ubilab-escape/mission-briefing/Briefing Clip/(Footage)/01. Edit Comp/Images/freelance-illustrator-peter-henderson-scifi.gif

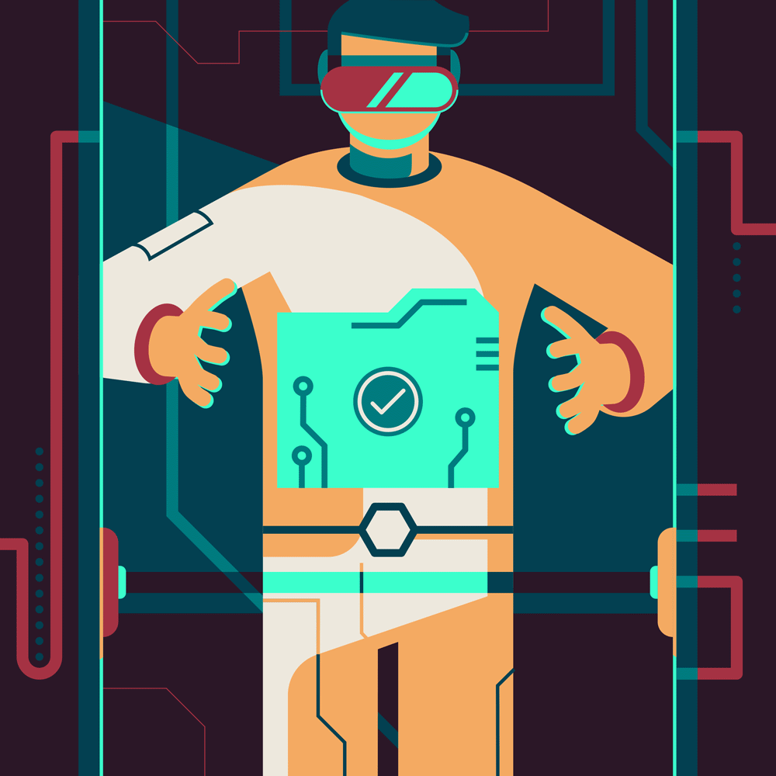
Briefing Clip/(Footage)/01. Edit Comp/Images/freelance-illustrator-peter-henderson-scifi.gif
