ubilab-escape/mission-briefing/CAD/Images/1.PNG

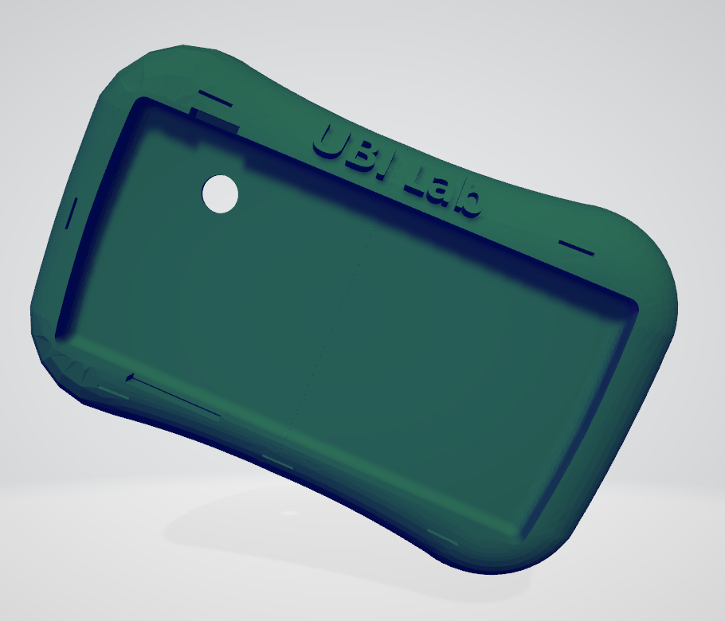
CAD/Images/1.PNG
