ubilab-escape/mission-briefing/CAD/Images/2.PNG

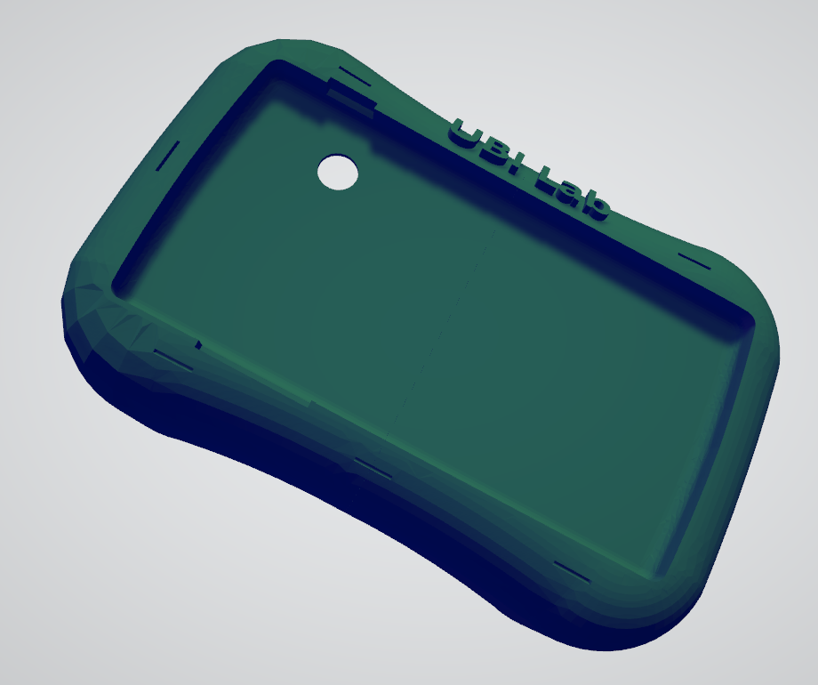
CAD/Images/2.PNG
