ubilab-escape/mission-briefing/CAD/Images/3.PNG

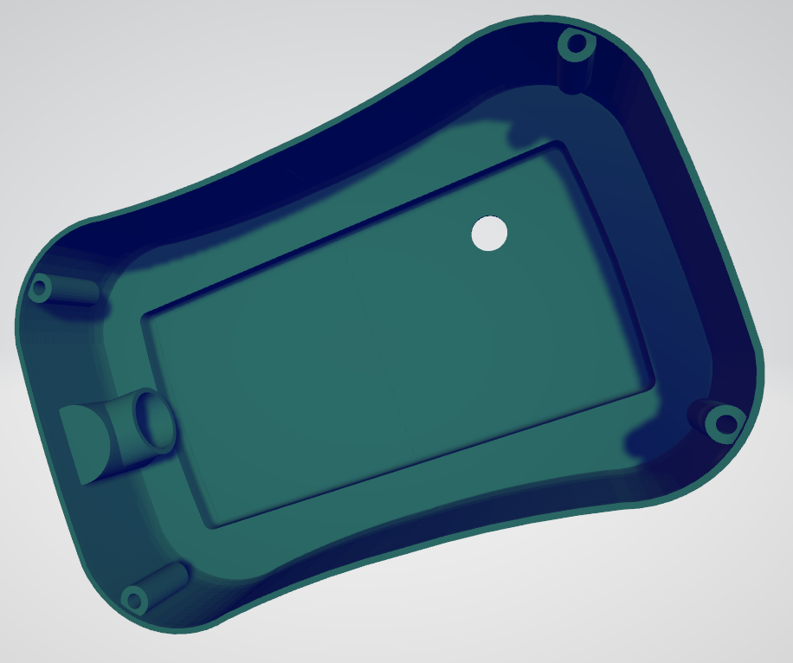
CAD/Images/3.PNG
