ubilab-escape/mission-briefing/CAD/Images/4.PNG

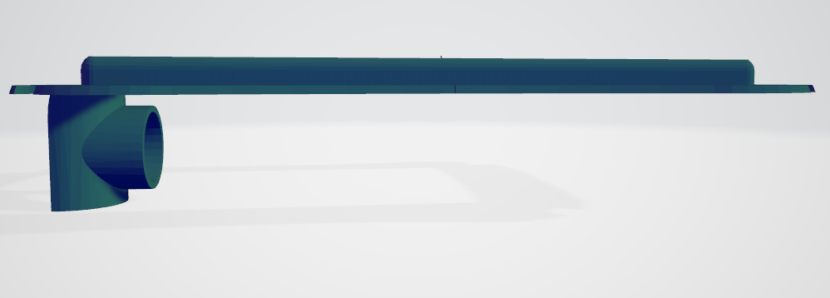
CAD/Images/4.PNG
