ubilab-escape/mission-briefing/CAD/Images/5.PNG

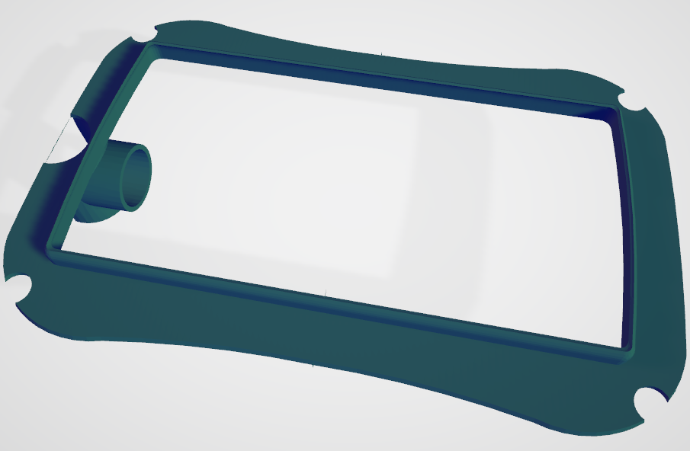
CAD/Images/5.PNG
