ubilab-escape/mission-briefing/CAD/Images/6.PNG

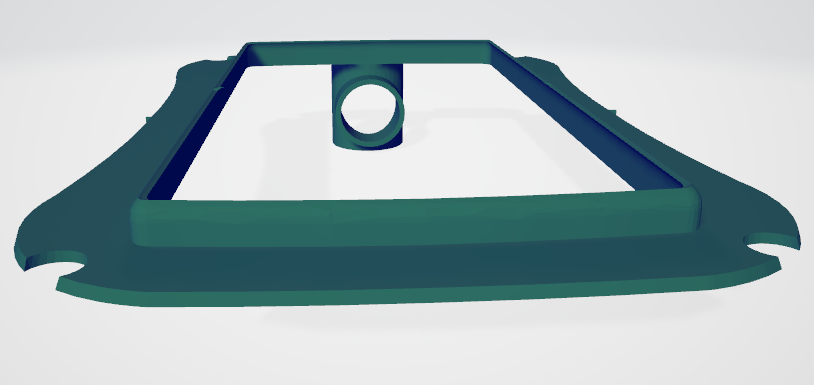
CAD/Images/6.PNG
