ubilab-escape/mission-briefing/CAD/Images/8.PNG

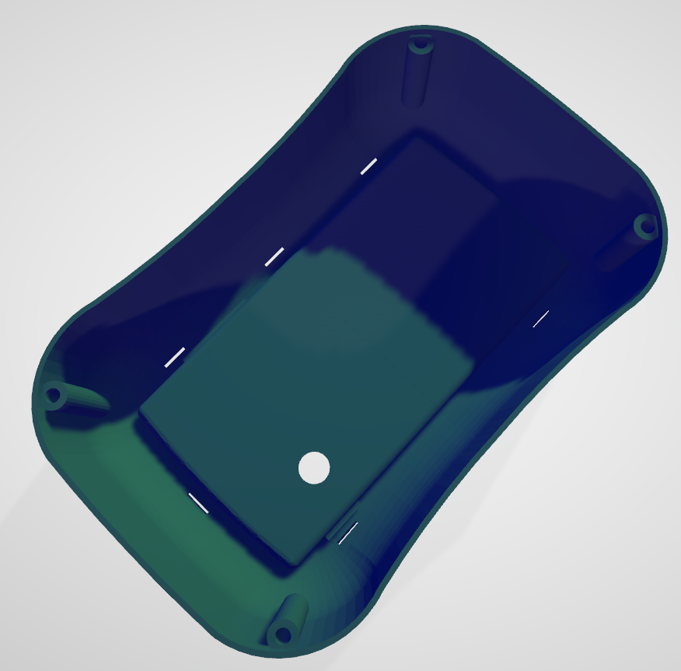
CAD/Images/8.PNG
