ubilab-escape/mission-briefing/CAD/Images/9.png

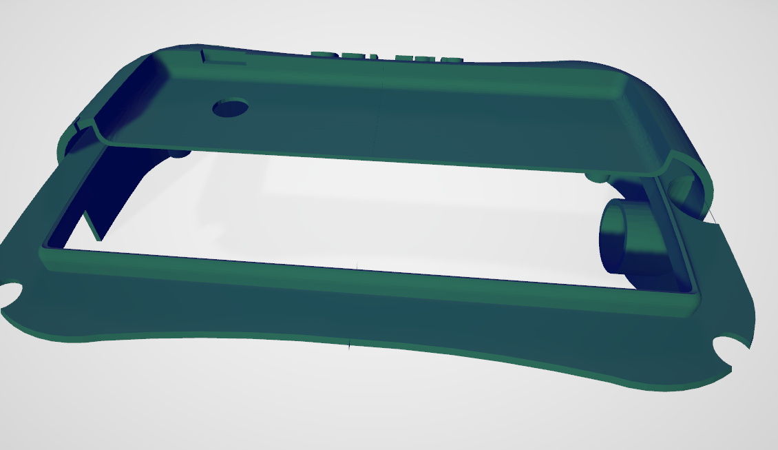
CAD/Images/9.png
